joshtyler/manila-ice/hdl/zephyr_test/src/picosoc.sv

/*
 *  PicoSoC - A simple example SoC using PicoRV32
 *
 *  Copyright (C) 2017  Clifford Wolf <clifford@clifford.at>
 *
 *  Permission to use, copy, modify, and/or distribute this software for any
 *  purpose with or without fee is hereby granted, provided that the above
 *  copyright notice and this permission notice appear in all copies.
 *
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
 */

`ifndef PICORV32_REGS
`ifdef PICORV32_V
`error "picosoc.v must be read before picorv32.v!"
`endif

`define PICORV32_REGS picosoc_regs
`endif

`ifndef PICOSOC_MEM
`define PICOSOC_MEM picosoc_mem
`endif

// this macro can be used to check if the verilog files in your
// design are read in the correct order.
`define PICOSOC_V

module picosoc (
	input clk,
	input resetn,

	output        iomem_valid,
	input         iomem_ready,
	output [ 3:0] iomem_wstrb,
	output [31:0] iomem_addr,
	output [31:0] iomem_wdata,
	input  [31:0] iomem_rdata,

	input  irq_5,
	input  irq_6,
	input  irq_7,

	output ser_tx,
	input  ser_rx,

	output flash_csb,
	output flash_clk,

	output flash_io0_oe,
	output flash_io1_oe,
	output flash_io2_oe,
	output flash_io3_oe,

	output flash_io0_do,
	output flash_io1_do,
	output flash_io2_do,
	output flash_io3_do,

	input  flash_io0_di,
	input  flash_io1_di,
	input  flash_io2_di,
	input  flash_io3_di
);
	parameter [0:0] BARREL_SHIFTER = 0;
	parameter [0:0] ENABLE_MULDIV = 0;
	parameter [0:0] ENABLE_COMPRESSED = 0;
	parameter [0:0] ENABLE_COUNTERS = 0;
	parameter [0:0] ENABLE_IRQ_QREGS = 0;

	parameter integer MEM_WORDS = 1;
	parameter [31:0] STACKADDR = (4*MEM_WORDS);       // end of memory
	parameter [31:0] PROGADDR_RESET = 32'h 0010_0000; // 1 MB into flash
	parameter [31:0] PROGADDR_IRQ = 32'h 0000_0000;

	reg [31:0] irq;
	wire irq_stall = 0;
	wire irq_uart = 0;

	always @* begin
		irq = 0;
		irq[3] = irq_stall;
		irq[4] = irq_uart;
		irq[5] = irq_5;
		irq[6] = irq_6;
		irq[7] = irq_7;
	end

	wire mem_valid;
	wire mem_instr;
	wire mem_ready;
	wire [31:0] mem_addr;
	wire [31:0] mem_wdata;
	wire [3:0] mem_wstrb;
	wire [31:0] mem_rdata;

	wire spimem_ready;
	wire [31:0] spimem_rdata;

	reg ram_ready;
	wire [31:0] ram_rdata;

	assign iomem_valid = mem_valid && (mem_addr[31:24] > 8'h 01);
	assign iomem_wstrb = mem_wstrb;
	assign iomem_addr = mem_addr;
	assign iomem_wdata = mem_wdata;

	wire spimemio_cfgreg_sel = mem_valid && (mem_addr == 32'h 0200_0000);
	wire [31:0] spimemio_cfgreg_do;

	wire        uart_tx_sel = (mem_valid && (mem_addr == 32'h 0200_0008)) ? mem_wstrb[0] : 1'b 0;
	wire        uart_tx_ready;

	wire        uart_rx_sel = (mem_valid && (mem_addr == 32'h 0200_0008)) ? (!mem_wstrb[0]) : 1'b 0;
	wire        uart_rx_valid;
	wire [31:0] uart_rx_data;

	assign mem_ready = (iomem_valid && iomem_ready) || spimem_ready || ram_ready || spimemio_cfgreg_sel ||
			(uart_tx_sel && uart_tx_ready) || (uart_rx_sel && uart_rx_valid);

	assign mem_rdata =
		(iomem_valid && iomem_ready) ? iomem_rdata :
		spimem_ready ? spimem_rdata :
		ram_ready ? ram_rdata :
		spimemio_cfgreg_sel ? spimemio_cfgreg_do :
		uart_tx_sel ? 32'h 0000_0000 : // Can't read from tx
		uart_rx_sel ? uart_rx_data :
		32'h 0000_0000;

	picorv32 #(
		.STACKADDR(STACKADDR),
		.PROGADDR_RESET(PROGADDR_RESET),
		.PROGADDR_IRQ(PROGADDR_IRQ),
		.BARREL_SHIFTER(BARREL_SHIFTER),
		.COMPRESSED_ISA(ENABLE_COMPRESSED),
		.ENABLE_COUNTERS(ENABLE_COUNTERS),
		.ENABLE_MUL(ENABLE_MULDIV),
		.ENABLE_DIV(ENABLE_MULDIV),
		.ENABLE_IRQ(1),
		.ENABLE_IRQ_QREGS(ENABLE_IRQ_QREGS)
	) cpu (
		.clk         (clk        ),
		.resetn      (resetn     ),
		.mem_valid   (mem_valid  ),
		.mem_instr   (mem_instr  ),
		.mem_ready   (mem_ready  ),
		.mem_addr    (mem_addr   ),
		.mem_wdata   (mem_wdata  ),
		.mem_wstrb   (mem_wstrb  ),
		.mem_rdata   (mem_rdata  ),
		.irq         (irq        )
	);

	spimemio spimemio (
		.clk    (clk),
		.resetn (resetn),
		.valid  (mem_valid && mem_addr >= 4*MEM_WORDS && mem_addr < 32'h 0200_0000),
		.ready  (spimem_ready),
		.addr   (mem_addr[23:0]),
		.rdata  (spimem_rdata),

		.flash_csb    (flash_csb   ),
		.flash_clk    (flash_clk   ),

		.flash_io0_oe (flash_io0_oe),
		.flash_io1_oe (flash_io1_oe),
		.flash_io2_oe (flash_io2_oe),
		.flash_io3_oe (flash_io3_oe),

		.flash_io0_do (flash_io0_do),
		.flash_io1_do (flash_io1_do),
		.flash_io2_do (flash_io2_do),
		.flash_io3_do (flash_io3_do),

		.flash_io0_di (flash_io0_di),
		.flash_io1_di (flash_io1_di),
		.flash_io2_di (flash_io2_di),
		.flash_io3_di (flash_io3_di),

		.cfgreg_we(spimemio_cfgreg_sel ? mem_wstrb : 4'b 0000),
		.cfgreg_di(mem_wdata),
		.cfgreg_do(spimemio_cfgreg_do)
	);

	uart_tx
	#(
		.CLK_FREQ(25000000),
		.BAUD_RATE(115200),
		.DATA_BITS(8)
	) uart_tx (
		.clk(clk),
		.sresetn(resetn),
		.serial_ready(1'b1),
		.serial_data(ser_tx),
		.s_axis_tready(uart_tx_ready),
		.s_axis_tvalid(uart_tx_sel),
		.s_axis_tdata(mem_wdata[7:0])
	);

	logic uart_rx_unbuf_valid;
	logic [7:0] uart_rx_unbuf_data;
	uart_rx
	#(
		.CLK_FREQ(25000000),
		.BAUD_RATE(115200),
		.DATA_BITS(8)
	) uart_rx (
		.clk(clk),
		.sresetn(resetn),
		.serial_data(ser_rx),
		.parallel_data_valid(uart_rx_unbuf_valid),
		.parallel_data(uart_rx_unbuf_data)
	);

	axis_register uart_rx_reg (
		.clk(clk),
		.sresetn(resetn),

		.axis_i_tready(),
		.axis_i_tvalid(uart_rx_unbuf_valid),
		.axis_i_tlast(1'b1),
		.axis_i_tdata(uart_rx_unbuf_data),
		.axis_i_tuser(1'b0),

		.axis_o_tready(uart_rx_sel),
		.axis_o_tvalid(uart_rx_valid),
		.axis_o_tlast(),
		.axis_o_tdata(uart_rx_data[7:0]),
		.axis_o_tuser()
	);
	assign uart_rx_data[31:8] = '0;

	always @(posedge clk)
		ram_ready <= mem_valid && !mem_ready && mem_addr < 4*MEM_WORDS;

	`PICOSOC_MEM #(
		.WORDS(MEM_WORDS)
	) memory (
		.clk(clk),
		.wen((mem_valid && !mem_ready && mem_addr < 4*MEM_WORDS) ? mem_wstrb : 4'b0),
		.addr(mem_addr[23:2]),
		.wdata(mem_wdata),
		.rdata(ram_rdata)
	);
endmodule

// Implementation note:
// Replace the following two modules with wrappers for your SRAM cells.

module picosoc_regs (
	input clk, wen,
	input [5:0] waddr,
	input [5:0] raddr1,
	input [5:0] raddr2,
	input [31:0] wdata,
	output [31:0] rdata1,
	output [31:0] rdata2
);
	reg [31:0] regs [0:31];

	always @(posedge clk)
		if (wen) regs[waddr[4:0]] <= wdata;

	assign rdata1 = regs[raddr1[4:0]];
	assign rdata2 = regs[raddr2[4:0]];
endmodule

module picosoc_mem #(
	parameter integer WORDS = 256
) (
	input clk,
	input [3:0] wen,
	input [21:0] addr,
	input [31:0] wdata,
	output reg [31:0] rdata
);
	reg [31:0] mem [0:WORDS-1];

	always @(posedge clk) begin
		rdata <= mem[addr];
		if (wen[0]) mem[addr][ 7: 0] <= wdata[ 7: 0];
		if (wen[1]) mem[addr][15: 8] <= wdata[15: 8];
		if (wen[2]) mem[addr][23:16] <= wdata[23:16];
		if (wen[3]) mem[addr][31:24] <= wdata[31:24];
	end
endmodule
