joshtyler/manila-ice/hdl/zephyr_test/src/pll.v

/**
 * PLL configuration
 *
 * This Verilog module was generated automatically
 * using the icepll tool from the IceStorm project.
 * Use at your own risk.
 *
 * Given input frequency:        50.000 MHz
 * Requested output frequency:   25.000 MHz
 * Achieved output frequency:    25.000 MHz
 */

module pll(
	input  clock_in,
	output clock_out,
	output locked
	);

`ifdef IVERILOG
	assign locked = 1;
	assign clock_out = clock_in;
`else
	SB_PLL40_CORE #(
			.FEEDBACK_PATH("SIMPLE"),
			.DIVR(4'b0000),		// DIVR =  0
			.DIVF(7'b0001111),	// DIVF = 15
			.DIVQ(3'b101),		// DIVQ =  5
			.FILTER_RANGE(3'b100)	// FILTER_RANGE = 4
		) uut (
			.LOCK(locked),
			.RESETB(1'b1),
			.BYPASS(1'b0),
			.REFERENCECLK(clock_in),
			.PLLOUTCORE(clock_out)
			);
`endif

endmodule
